yamamo2shun1/C4NDY/STM32CubeIDE/C4NDY_STK/Core/Inc/main.h

#define HC164_CLK_Pin       GPIO_PIN_13
#define HC164_CLK_GPIO_Port GPIOC
#define HC164_A_Pin         GPIO_PIN_14
#define HC164_A_GPIO_Port   GPIOC
#define HC165_CLK_Pin       GPIO_PIN_15
#define HC165_CLK_GPIO_Port GPIOC
#define USER_SW_Pin         GPIO_PIN_10
#define USER_SW_GPIO_Port   GPIOB
#define USER_LED_Pin        GPIO_PIN_12
#define USER_LED_GPIO_Port  GPIOB
#define LP_LED_Pin          GPIO_PIN_13
#define LP_LED_GPIO_Port    GPIOB
#define HC165_SL_Pin        GPIO_PIN_7
#define HC165_SL_GPIO_Port  GPIOB
#define HC165_QH_Pin        GPIO_PIN_9
#define HC165_QH_GPIO_Port  GPIOB
