yamamo2shun1/C4NDY/STM32CubeIDE/C4NDY_KeyVLM/Core/Inc/tusb_config.h

/*
 * The MIT License (MIT)
 *
 * Copyright (c) 2019 Ha Thach (tinyusb.org)
 *
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
 */

#ifndef _TUSB_CONFIG_H_
#define _TUSB_CONFIG_H_

#ifdef __cplusplus
extern "C"
{
#endif

#include "usb_descriptors.h"

//--------------------------------------------------------------------+
// Board Specific Configuration
//--------------------------------------------------------------------+
#define CFG_TUSB_MCU              OPT_MCU_STM32G4
#define CFG_TUSB_OS               OPT_OS_NONE
#define BOARD_DEVICE_RHPORT_SPEED OPT_MODE_FULL_SPEED
#define BOARD_TUD_MAX_SPEED       OPT_MODE_FULL_SPEED
#define BOARD_DEVICE_RHPORT_NUM   0
#define BOARD_TUD_RHPORT          0
#define CFG_TUSB_RHPORT0_MODE     (OPT_MODE_DEVICE | OPT_MODE_FULL_SPEED)
// #define CFG_TUSB_DEBUG            2

// RHPort number used for device can be defined by board.mk, default to port 0
#ifndef BOARD_TUD_RHPORT
    #define BOARD_TUD_RHPORT 0
#endif

// RHPort max operational speed can defined by board.mk
#ifndef BOARD_TUD_MAX_SPEED
    #define BOARD_TUD_MAX_SPEED OPT_MODE_DEFAULT_SPEED
#endif

//--------------------------------------------------------------------
// COMMON CONFIGURATION
//--------------------------------------------------------------------

// defined by compiler flags for flexibility
#ifndef CFG_TUSB_MCU
    #error CFG_TUSB_MCU must be defined
#endif

#ifndef CFG_TUSB_OS
    #define CFG_TUSB_OS OPT_OS_NONE
#endif

#ifndef CFG_TUSB_DEBUG
    #define CFG_TUSB_DEBUG 0
#endif

// Enable Device stack
#define CFG_TUD_ENABLED 1

// Default is max speed that hardware controller could support with on-chip PHY
#define CFG_TUD_MAX_SPEED BOARD_TUD_MAX_SPEED

/* USB DMA on some MCUs can only access a specific SRAM region with restriction on alignment.
 * Tinyusb use follows macros to declare transferring memory so that they can be put
 * into those specific section.
 * e.g
 * - CFG_TUSB_MEM SECTION : __attribute__ (( section(".usb_ram") ))
 * - CFG_TUSB_MEM_ALIGN   : __attribute__ ((aligned(4)))
 */
#ifndef CFG_TUSB_MEM_SECTION
    #define CFG_TUSB_MEM_SECTION
#endif

#ifndef CFG_TUSB_MEM_ALIGN
    #define CFG_TUSB_MEM_ALIGN __attribute__((aligned(4)))
#endif

    //--------------------------------------------------------------------
    // DEVICE CONFIGURATION
    //--------------------------------------------------------------------

#ifndef CFG_TUD_ENDPOINT0_SIZE
    #define CFG_TUD_ENDPOINT0_SIZE 64
#endif

//------------- CLASS -------------//
#define CFG_TUD_AUDIO  1
#define CFG_TUD_HID    2
#define CFG_TUD_CDC    0
#define CFG_TUD_MSC    0
#define CFG_TUD_MIDI   0
#define CFG_TUD_VENDOR 0

// HID buffer size Should be sufficient to hold ID (if any) + Data
#define CFG_TUD_HID_EP_BUFSIZE 32

    //--------------------------------------------------------------------
    // AUDIO CLASS DRIVER CONFIGURATION
    //--------------------------------------------------------------------

#define __RX__

#define CFG_TUD_AUDIO_FUNC_1_DESC_LEN TUD_AUDIO_HEADPHONE_STEREO_DESC_LEN

// Audio format type I specifications
#define CFG_TUD_AUDIO_FUNC_1_MAX_SAMPLE_RATE 48000

#define CFG_TUD_AUDIO_FUNC_1_N_CHANNELS_RX 2

// 24bit in 32bit slots
#define CFG_TUD_AUDIO_FUNC_1_N_BYTES_PER_SAMPLE_RX 4
#define CFG_TUD_AUDIO_FUNC_1_RESOLUTION_RX         24

// EP and buffer size - for isochronous EP´s, the buffer and EP size are equal (different sizes would not make sense)
#define CFG_TUD_AUDIO_ENABLE_EP_OUT      1
#define CFG_TUD_AUDIO_ENABLE_FEEDBACK_EP 1

#define CFG_TUD_AUDIO_FUNC_1_EP_OUT_SZ_MAX    512  // TUD_AUDIO_EP_SIZE(CFG_TUD_AUDIO_FUNC_1_MAX_SAMPLE_RATE, CFG_TUD_AUDIO_FUNC_1_N_BYTES_PER_SAMPLE_RX, CFG_TUD_AUDIO_FUNC_1_N_CHANNELS_RX)
#define CFG_TUD_AUDIO_FUNC_1_EP_OUT_SW_BUF_SZ CFG_TUD_AUDIO_FUNC_1_EP_OUT_SZ_MAX * 4

// Number of Standard AS Interface Descriptors (4.9.1) defined per audio function - this is required to be able to remember the current alternate settings of these interfaces - We restrict us here to have a constant number for all audio functions (which means this has to be the maximum number of AS interfaces an audio function has and a second audio function with less AS interfaces just wastes a few bytes)
#define CFG_TUD_AUDIO_FUNC_1_N_AS_INT 2

// Size of control request buffer
#define CFG_TUD_AUDIO_FUNC_1_CTRL_BUF_SZ 64

#ifdef __cplusplus
}
#endif

#endif /* _TUSB_CONFIG_H_ */
