yamamo2shun1/C4NDY/STM32CubeIDE/C4NDY_STK/Core/Src/icled.c

/*
 * icled.c
 *
 *  Created on: Aug 7, 2024
 *      Author: shun
 */

#include "icled.h"

#include "sai.h"
#include "keyboard.h"
#include "tim.h"

RGB_Color_t rgb_normal[2] = {
    {0x00, 0x00, 0x00},
    {0x00, 0x00, 0x00}
};
RGB_Color_t rgb_upper[2] = {
    {0x00, 0x00, 0x00},
    {0x00, 0x00, 0x00}
};
RGB_Color_t rgb_shift[2] = {
    {0x00, 0x00, 0x00},
    {0x00, 0x00, 0x00}
};
RGB_Color_t rgb_blank = {0x00, 0x00, 0x00};

double intensity[2] = {1.0, 1.0};

uint8_t grb_prev[LED_NUMS][RGB]    = {0};
uint8_t grb_current[LED_NUMS][RGB] = {0};
uint8_t grb[LED_NUMS][RGB]         = {0};

uint32_t led_buf[LED_NUMS * RGB * COL_BITS + 1]      = {0};
uint32_t led_buf_prev[LED_NUMS * RGB * COL_BITS + 1] = {0};

uint32_t counter = 0;

bool isLeftMarked     = false;
int countLeftMark     = 0;
double fadeLeftMark   = 0.0;
uint8_t stateLeftMark = 0;

bool isRightMarked     = false;
int countRightMark     = 0;
double fadeRightMark   = 0.0;
uint8_t stateRightMark = 0;

bool isMouseMarked     = false;
int countMouseMark     = 0;
double fadeMouseMark   = 0.0;
uint8_t stateMouseMark = 4;

bool isMixMarked     = false;
int countMixMark     = 0;
double fadeMixMark   = 0.0;
uint8_t stateMixMark = 4;

void HAL_TIM_PWM_PulseFinishedCallback(TIM_HandleTypeDef* htim)
{
    HAL_TIM_PWM_Stop_DMA(htim, TIM_CHANNEL_1);
}

void setNormalColor(const uint8_t keymapId, const uint8_t r, const uint8_t g, const uint8_t b)
{
    rgb_normal[keymapId].r = r;
    rgb_normal[keymapId].g = g;
    rgb_normal[keymapId].b = b;
}

void setUpperColor(const uint8_t keymapId, const uint8_t r, const uint8_t g, const uint8_t b)
{
    rgb_upper[keymapId].r = r;
    rgb_upper[keymapId].g = g;
    rgb_upper[keymapId].b = b;
}

void setShiftColor(const uint8_t keymapId, const uint8_t r, const uint8_t g, const uint8_t b)
{
    rgb_shift[keymapId].r = r;
    rgb_shift[keymapId].g = g;
    rgb_shift[keymapId].b = b;
}

RGB_Color_t getNormalColor(const uint8_t keymapId)
{
    return rgb_normal[keymapId];
}

RGB_Color_t getUpperColor(const uint8_t keymapId)
{
    return rgb_upper[keymapId];
}

RGB_Color_t getShiftColor(const uint8_t keymapId)
{
    return rgb_shift[keymapId];
}

RGB_Color_t getBlankColor(void)
{
    return rgb_blank;
}

void setIntensity(const uint8_t keymapId, const uint8_t value)
{
    intensity[keymapId] = (double) value / 255.0;
}

double getIntensity(const uint8_t keymapId)
{
    return intensity[keymapId];
}

RGB_Color_t gradation(const RGB_Color_t color1, const RGB_Color_t color2, const double rate)
{
    const uint8_t r         = (uint8_t) ((double) (color2.r - color1.r) * rate + (double) color1.r);
    const uint8_t g         = (uint8_t) ((double) (color2.g - color1.g) * rate + (double) color1.g);
    const uint8_t b         = (uint8_t) ((double) (color2.b - color1.b) * rate + (double) color1.b);
    const RGB_Color_t color = {r, g, b};
    return color;
}

void setLedBufDirect(const uint8_t index, const RGB_Color_t rgb_color)
{
    grb[index][0] = rgb_color.g;
    grb[index][1] = rgb_color.r;
    grb[index][2] = rgb_color.b;
}

void setAllLedBufDirect(const RGB_Color_t rgb_color)
{
    for (int i = 0; i < LED_NUMS; i++)
    {
        grb[i][0] = rgb_color.g;
        grb[i][1] = rgb_color.r;
        grb[i][2] = rgb_color.b;
    }
}

void setColumnColorLedBuf(const uint8_t row, const uint16_t column, const double fade)
{
    const RGB_Color_t bc = rgb_normal[getKeymapID()];
    const RGB_Color_t c  = gradation(rgb_normal[getKeymapID()], rgb_upper[getKeymapID()], fade);

    for (int i = 0; i < 10; i++)
    {
        if ((column >> (9 - i)) & 0x01)
        {
            setLedBufDirect(i + row * 10, c);
        }
        else
        {
            setLedBufDirect(i + row * 10, bc);
        }
    }
}

void setLeftHalfColumnColorLedBuf(const uint8_t row, const uint16_t column, const double fade)
{
    const RGB_Color_t bc = rgb_normal[getKeymapID()];
    const RGB_Color_t c  = gradation(rgb_normal[getKeymapID()], rgb_upper[getKeymapID()], fade);

    for (int i = 0; i < 5; i++)
    {
        if ((column >> (9 - i)) & 0x01)
        {
            setLedBufDirect(i + row * 10, c);
        }
        else
        {
            setLedBufDirect(i + row * 10, bc);
        }
    }
}

void setRightHalfColumnColorLedBuf(const uint8_t row, const uint16_t column, const double fade)
{
    const RGB_Color_t bc = rgb_normal[getKeymapID()];
    const RGB_Color_t c  = gradation(rgb_normal[getKeymapID()], rgb_upper[getKeymapID()], fade);

    for (int i = 5; i < 10; i++)
    {
        if ((column >> (9 - i)) & 0x01)
        {
            setLedBufDirect(i + row * 10, c);
        }
        else
        {
            setLedBufDirect(i + row * 10, bc);
        }
    }
}

void setLedMarkForJoystick(const uint8_t index, const uint8_t state)
{
    // SEGGER_RTT_printf(0, "set: %d, %d, %d\n", index, state, isLeftMarked);

    if (index == 0)
    {
        switch (state)
        {
        case 0:
            setLeftHalfColumnColorLedBuf(0, 0b0110000000, fadeLeftMark);
            setLeftHalfColumnColorLedBuf(1, 0b0100000000, fadeLeftMark);
            setLeftHalfColumnColorLedBuf(2, 0b0000000000, fadeLeftMark);
            break;
        case 1:
            setLeftHalfColumnColorLedBuf(0, 0b0010000000, fadeLeftMark);
            setLeftHalfColumnColorLedBuf(1, 0b0101000000, fadeLeftMark);
            setLeftHalfColumnColorLedBuf(2, 0b0000000000, fadeLeftMark);
            break;
        case 2:
            setLeftHalfColumnColorLedBuf(0, 0b0011000000, fadeLeftMark);
            setLeftHalfColumnColorLedBuf(1, 0b0001000000, fadeLeftMark);
            setLeftHalfColumnColorLedBuf(2, 0b0000000000, fadeLeftMark);
            break;
        case 3:
            setLeftHalfColumnColorLedBuf(0, 0b0010000000, fadeLeftMark);
            setLeftHalfColumnColorLedBuf(1, 0b0100000000, fadeLeftMark);
            setLeftHalfColumnColorLedBuf(2, 0b0010000000, fadeLeftMark);
            break;
        case 5:
            setLeftHalfColumnColorLedBuf(0, 0b0010000000, fadeLeftMark);
            setLeftHalfColumnColorLedBuf(1, 0b0001000000, fadeLeftMark);
            setLeftHalfColumnColorLedBuf(2, 0b0010000000, fadeLeftMark);
            break;
        case 6:
            setLeftHalfColumnColorLedBuf(0, 0b0000000000, fadeLeftMark);
            setLeftHalfColumnColorLedBuf(1, 0b0100000000, fadeLeftMark);
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
                {
                    isRenewed = true;
                }

                led_buf_prev[j * WL_LED_BIT_LEN + i + COL_BITS * k] = led_buf[j * WL_LED_BIT_LEN + i + COL_BITS * k];
            }
        }
    }
    led_buf[DMA_BUF_SIZE - 1] = 0;

    if (isRenewed)
    {
        if (hsai_BlockB1.State != HAL_SAI_STATE_BUSY)
        {
            HAL_TIM_PWM_Start_DMA(&htim8, TIM_CHANNEL_1, (uint32_t*) led_buf, DMA_BUF_SIZE);
        }
    }
}

void checkColor(const uint8_t r, const uint8_t g, const uint8_t b)
{
    const RGB_Color_t rgb_check = {r, g, b};

    SEGGER_RTT_printf(0, "(r, g, b) = (%02X, %02X, %02X)\n", r, g, b);

    setAllLedBufDirect(rgb_check);
    renew();
}

void loadLEDColorsFromFlash(void)
{
    SEGGER_RTT_printf(0, "// LED\n");
    SEGGER_RTT_printf(0, "[ ");
    setNormalColor(0, read_flash_data(BASIC_PARAMS_NUM + (8 * MATRIX_ROWS * MATRIX_COLUMNS) + (4 * STICK_NUM * STICK_DIRECTION) + 0), read_flash_data(BASIC_PARAMS_NUM + (8 * MATRIX_ROWS * MATRIX_COLUMNS) + (4 * STICK_NUM * STICK_DIRECTION) + 1), read_flash_data(BASIC_PARAMS_NUM + (8 * MATRIX_ROWS * MATRIX_COLUMNS) + (4 * STICK_NUM * STICK_DIRECTION) + 2));
    SEGGER_RTT_printf(0, "%02X ", read_flash_data(BASIC_PARAMS_NUM + (8 * MATRIX_ROWS * MATRIX_COLUMNS) + (4 * STICK_NUM * STICK_DIRECTION) + 0));
    SEGGER_RTT_printf(0, "%02X ", read_flash_data(BASIC_PARAMS_NUM + (8 * MATRIX_ROWS * MATRIX_COLUMNS) + (4 * STICK_NUM * STICK_DIRECTION) + 1));
    SEGGER_RTT_printf(0, "%02X ", read_flash_data(BASIC_PARAMS_NUM + (8 * MATRIX_ROWS * MATRIX_COLUMNS) + (4 * STICK_NUM * STICK_DIRECTION) + 2));
    SEGGER_RTT_printf(0, "]\n");

    SEGGER_RTT_printf(0, "[ ");
    setUpperColor(0, read_flash_data(BASIC_PARAMS_NUM + (8 * MATRIX_ROWS * MATRIX_COLUMNS) + (4 * STICK_NUM * STICK_DIRECTION) + 3), read_flash_data(BASIC_PARAMS_NUM + (8 * MATRIX_ROWS * MATRIX_COLUMNS) + (4 * STICK_NUM * STICK_DIRECTION) + 4), read_flash_data(BASIC_PARAMS_NUM + (8 * MATRIX_ROWS * MATRIX_COLUMNS) + (4 * STICK_NUM * STICK_DIRECTION) + 5));
    SEGGER_RTT_printf(0, "%02X ", read_flash_data(BASIC_PARAMS_NUM + (8 * MATRIX_ROWS * MATRIX_COLUMNS) + (4 * STICK_NUM * STICK_DIRECTION) + 3));
    SEGGER_RTT_printf(0, "%02X ", read_flash_data(BASIC_PARAMS_NUM + (8 * MATRIX_ROWS * MATRIX_COLUMNS) + (4 * STICK_NUM * STICK_DIRECTION) + 4));
    SEGGER_RTT_printf(0, "%02X ", read_flash_data(BASIC_PARAMS_NUM + (8 * MATRIX_ROWS * MATRIX_COLUMNS) + (4 * STICK_NUM * STICK_DIRECTION) + 5));
    SEGGER_RTT_printf(0, "]\n");

    SEGGER_RTT_printf(0, "[ ");
    setShiftColor(0, read_flash_data(BASIC_PARAMS_NUM + (8 * MATRIX_ROWS * MATRIX_COLUMNS) + (4 * STICK_NUM * STICK_DIRECTION) + 6), read_flash_data(BASIC_PARAMS_NUM + (8 * MATRIX_ROWS * MATRIX_COLUMNS) + (4 * STICK_NUM * STICK_DIRECTION) + 7), read_flash_data(BASIC_PARAMS_NUM + (8 * MATRIX_ROWS * MATRIX_COLUMNS) + (4 * STICK_NUM * STICK_DIRECTION) + 8));
    SEGGER_RTT_printf(0, "%02X ", read_flash_data(BASIC_PARAMS_NUM + (8 * MATRIX_ROWS * MATRIX_COLUMNS) + (4 * STICK_NUM * STICK_DIRECTION) + 6));
    SEGGER_RTT_printf(0, "%02X ", read_flash_data(BASIC_PARAMS_NUM + (8 * MATRIX_ROWS * MATRIX_COLUMNS) + (4 * STICK_NUM * STICK_DIRECTION) + 7));
    SEGGER_RTT_printf(0, "%02X ", read_flash_data(BASIC_PARAMS_NUM + (8 * MATRIX_ROWS * MATRIX_COLUMNS) + (4 * STICK_NUM * STICK_DIRECTION) + 8));
    SEGGER_RTT_printf(0, "]\n");
    SEGGER_RTT_printf(0, "\n");

    SEGGER_RTT_printf(0, "[ ");
    setNormalColor(1, read_flash_data(BASIC_PARAMS_NUM + (8 * MATRIX_ROWS * MATRIX_COLUMNS) + (4 * STICK_NUM * STICK_DIRECTION) + 9), read_flash_data(BASIC_PARAMS_NUM + (8 * MATRIX_ROWS * MATRIX_COLUMNS) + (4 * STICK_NUM * STICK_DIRECTION) + 10), read_flash_data(BASIC_PARAMS_NUM + (8 * MATRIX_ROWS * MATRIX_COLUMNS) + (4 * STICK_NUM * STICK_DIRECTION) + 11));
    SEGGER_RTT_printf(0, "%02X ", read_flash_data(BASIC_PARAMS_NUM + (8 * MATRIX_ROWS * MATRIX_COLUMNS) + (4 * STICK_NUM * STICK_DIRECTION) + 9));
    SEGGER_RTT_printf(0, "%02X ", read_flash_data(BASIC_PARAMS_NUM + (8 * MATRIX_ROWS * MATRIX_COLUMNS) + (4 * STICK_NUM * STICK_DIRECTION) + 10));
    SEGGER_RTT_printf(0, "%02X ", read_flash_data(BASIC_PARAMS_NUM + (8 * MATRIX_ROWS * MATRIX_COLUMNS) + (4 * STICK_NUM * STICK_DIRECTION) + 11));
    SEGGER_RTT_printf(0, "]\n");

    SEGGER_RTT_printf(0, "[ ");
    setUpperColor(1, read_flash_data(BASIC_PARAMS_NUM + (8 * MATRIX_ROWS * MATRIX_COLUMNS) + (4 * STICK_NUM * STICK_DIRECTION) + 12), read_flash_data(BASIC_PARAMS_NUM + (8 * MATRIX_ROWS * MATRIX_COLUMNS) + (4 * STICK_NUM * STICK_DIRECTION) + 13), read_flash_data(BASIC_PARAMS_NUM + (8 * MATRIX_ROWS * MATRIX_COLUMNS) + (4 * STICK_NUM * STICK_DIRECTION) + 14));
    SEGGER_RTT_printf(0, "%02X ", read_flash_data(BASIC_PARAMS_NUM + (8 * MATRIX_ROWS * MATRIX_COLUMNS) + (4 * STICK_NUM * STICK_DIRECTION) + 12));
    SEGGER_RTT_printf(0, "%02X ", read_flash_data(BASIC_PARAMS_NUM + (8 * MATRIX_ROWS * MATRIX_COLUMNS) + (4 * STICK_NUM * STICK_DIRECTION) + 13));
    SEGGER_RTT_printf(0, "%02X ", read_flash_data(BASIC_PARAMS_NUM + (8 * MATRIX_ROWS * MATRIX_COLUMNS) + (4 * STICK_NUM * STICK_DIRECTION) + 14));
    SEGGER_RTT_printf(0, "]\n");

    SEGGER_RTT_printf(0, "[ ");
    setShiftColor(1, read_flash_data(BASIC_PARAMS_NUM + (8 * MATRIX_ROWS * MATRIX_COLUMNS) + (4 * STICK_NUM * STICK_DIRECTION) + 15), read_flash_data(BASIC_PARAMS_NUM + (8 * MATRIX_ROWS * MATRIX_COLUMNS) + (4 * STICK_NUM * STICK_DIRECTION) + 16), read_flash_data(BASIC_PARAMS_NUM + (8 * MATRIX_ROWS * MATRIX_COLUMNS) + (4 * STICK_NUM * STICK_DIRECTION) + 17));
    SEGGER_RTT_printf(0, "%02X ", read_flash_data(BASIC_PARAMS_NUM + (8 * MATRIX_ROWS * MATRIX_COLUMNS) + (4 * STICK_NUM * STICK_DIRECTION) + 15));
    SEGGER_RTT_printf(0, "%02X ", read_flash_data(BASIC_PARAMS_NUM + (8 * MATRIX_ROWS * MATRIX_COLUMNS) + (4 * STICK_NUM * STICK_DIRECTION) + 16));
    SEGGER_RTT_printf(0, "%02X ", read_flash_data(BASIC_PARAMS_NUM + (8 * MATRIX_ROWS * MATRIX_COLUMNS) + (4 * STICK_NUM * STICK_DIRECTION) + 17));
    SEGGER_RTT_printf(0, "]\n");

    setAllLedBufDirect(rgb_normal[getKeymapID()]);
    setLedBufDirect(30, rgb_upper[getKeymapID()]);
    setLedBufDirect(31, rgb_upper[getKeymapID()]);
    setLedBufDirect(32, rgb_upper[getKeymapID()]);
    setLedBufDirect(33, rgb_upper[getKeymapID()]);
    renew();

    SEGGER_RTT_printf(0, "// LED\n");
    SEGGER_RTT_printf(0, "[ ");
    setIntensity(0, read_flash_data(3));
    setIntensity(1, read_flash_data(4));
    SEGGER_RTT_printf(0, "%d ", read_flash_data(3));
    SEGGER_RTT_printf(0, "%d ", read_flash_data(4));
    SEGGER_RTT_printf(0, "]\n");
}

void setMark(const uint8_t index, const uint8_t state)
{
    SEGGER_RTT_printf(0, "setMark(%d, %d)\n", index, state);

    if (isMixMarked)
    {
        //fadeMixMark = 0.0;
        isMixMarked = false;
        setLedMarkForMix(255);
        HAL_Delay(5);
    }

    if (index == 0)
    {
        isLeftMarked  = false;
        countLeftMark = 0;
        fadeLeftMark  = 1.0;
        stateLeftMark = state;
        setLedMarkForJoystick(0, stateLeftMark);
    }
    else if (index == 1)
    {
        isMouseMarked  = false;

        isRightMarked  = false;
        countRightMark = 0;
        fadeRightMark  = 1.0;
        stateRightMark = state;
        setLedMarkForJoystick(1, stateRightMark);
    }
}

void clearMark(const uint8_t index, const uint8_t state)
{
    SEGGER_RTT_printf(0, "clearMark(%d, %d)\n", index, state);
    if (index == 0)
    {
        isLeftMarked  = true;
        countLeftMark = 0;
        fadeLeftMark  = 1.0;
        stateLeftMark = state;
        setLedMarkForJoystick(0, stateLeftMark);
    }
    else if (index == 1)
    {
        isRightMarked  = true;
        countRightMark = 0;
        fadeRightMark  = 1.0;
        stateRightMark = state;
        setLedMarkForJoystick(1, stateRightMark);
    }
}

void setMouseMark(const uint8_t state)
{
    isMixMarked = false;

    isMouseMarked  = false;
    countMouseMark = 0;
    fadeMouseMark  = 1.0;
    stateMouseMark = state;
    setLedMouseMarkForJoystick(stateMouseMark);
}

void clearMouseMark(void)
{
    isMouseMarked  = true;
    countMouseMark = 0;
    fadeMouseMark  = 1.0;
    setLedMouseMarkForJoystick(stateMouseMark);
}

void setMixMark(const uint16_t xfade)
{
    isLeftMarked  = false;
    isRightMarked = false;
    isMouseMarked = false;

    isMixMarked  = true;
    countMixMark = 0;
    fadeMixMark  = 1.0;
    stateMixMark = (xfade + 64) >> 7;
    setLedMarkForMix(stateMixMark);
}

void led_control_task(void)
{
    if (isLeftMarked)
    {
        countLeftMark++;
        if (countLeftMark > ANIMATION_COUNT_MAX)
        {
            countLeftMark = 0;

            setLedMarkForJoystick(0, stateLeftMark);

            fadeLeftMark -= 0.075;
            if (fadeLeftMark <= 0)
            {
                fadeLeftMark = 0;
                isLeftMarked = false;
            }
        }
    }

    if (isRightMarked)
    {
        countRightMark++;
        if (countRightMark > ANIMATION_COUNT_MAX)
        {
            countRightMark = 0;

            setLedMarkForJoystick(1, stateRightMark);

            fadeRightMark -= 0.075;
            if (fadeRightMark <= 0)
            {
                fadeRightMark  = 0.0;
                isRightMarked  = false;
                stateMouseMark = 4;
            }
        }
    }

    if (isMouseMarked)
    {
        countMouseMark++;
        if (countMouseMark > ANIMATION_COUNT_MAX)
        {
            countMouseMark = 0;

            setLedMouseMarkForJoystick(stateMouseMark);

            fadeMouseMark -= 0.075;
            if (fadeMouseMark <= 0)
            {
                fadeMouseMark  = 0.0;
                isMouseMarked  = false;
                stateMouseMark = 4;
            }
        }
    }

    if (isMixMarked)
    {
        countMixMark++;
        if (countMixMark > ANIMATION_COUNT_MAX)
        {
            countMixMark = 0;

            setLedMarkForMix(stateMixMark);

            fadeMixMark -= 0.075;
            if (fadeMixMark <= 0)
            {
                fadeMixMark  = 0.0;
                isMixMarked  = false;
                stateMixMark = 4;
            }
        }
    }
}
