yamamo2shun1/C4NDY/STM32CubeIDE/C4NDY_STK/Core/Inc/icled.h

/*
 * icled.h
 *
 *  Created on: Aug 7, 2024
 *      Author: shun
 */

#ifndef INC_ICLED_H_
#define INC_ICLED_H_

#include <stdint.h>

#define RGB      3
#define COL_BITS 8

#define WL_LED_BIT_LEN (RGB * COL_BITS)  // g:8,r:8,b:8
#define WL_LED_ONE     12
#define WL_LED_ZERO    4

#define LED_NUMS 34

#define GRADATION_RATE_STEP 0.2
#define GRADATION_COUNT_MAX 5

#define ANIMATION_COUNT_MAX 30

#define DMA_BUF_SIZE (LED_NUMS * WL_LED_BIT_LEN + 1)

typedef struct
{
    uint8_t r;
    uint8_t g;
    uint8_t b;
} RGB_Color_t;

void setNormalColor(const uint8_t keymapId, const uint8_t r, const uint8_t g, const uint8_t b);
void setUpperColor(const uint8_t keymapId, const uint8_t r, const uint8_t g, const uint8_t b);
void setShiftColor(const uint8_t keymapId, const uint8_t r, const uint8_t g, const uint8_t b);
RGB_Color_t getNormalColor(const uint8_t keymapId);
RGB_Color_t getUpperColor(const uint8_t keymapId);
RGB_Color_t getShiftColor(const uint8_t keymapId);
RGB_Color_t getBlankColor(void);

void setIntensity(const uint8_t keymapId, const uint8_t value);
double getIntensity(const uint8_t keymapId);

void renew(void);

void checkColor(const uint8_t r, const uint8_t g, const uint8_t b);

void loadLEDColorsFromFlash(void);

void setMark(const uint8_t index, const uint8_t state);
void clearMark(const uint8_t index, const uint8_t state);
void setMouseMark(const uint8_t state);
void clearMouseMark(void);
void setMixMark(const uint16_t xfade);

void led_control_task(void);

#endif /* INC_ICLED_H_ */
